quichedood/DAWA-7.x/03-DEV/src/tft.cpp

/*
@file    tft.c
@brief   TFT handling functions for EVE_Test project
@version 1.13
@date    2020-09-05
@author  Rudolph Riedel

@section History

1.0
- initial release

1.1
- added a simple .png image that is drawn beneath the clock just as example of how it could be done

1.2
- replaced the clock with a scrolling line-strip
- moved the .png image over to the font-test section to make room
- added a scrolling bar display
- made scrolling depending on the state of the on/off button
- reduced the precision of VERTEX2F to 1 Pixel with VERTEXT_FORMAT() (FT81x only) to avoid some pointless "*16" multiplications

1.3
- adapted to release 3 of Ft8xx library with EVE_ and ft_ prefixes changed to EVE_
- removed "while (EVE_busy());" lines after EVE_cmd_execute() since it does that by itself now
- removed "EVE_cmd_execute();" line after EVE_cmd_loadimage(MEM_PIC1, EVE_OPT_NODL, pngpic, pngpic_size); as EVE_cmd_loadimage() executes itself now

1.4
- added num_profile_a and num_profile_b for simple profiling
- utilised EVE_cmd_start()
- some general cleanup and house-keeping to make it fit for release

1.5
- simplified the example layout a lot and made it to scale with all display-sizes

1.6
- a bit of house-keeping after trying a couple of things

1.7
- added a display for the amount of bytes generated in the display-list by the command co-pro

1.8
- moved the color settings from EVE_config.h to here

1.9
- changed FT8_ prefixes to EVE_

1.10
- some cleanup

1.11
- updated to be more similar to what I am currently using in projects

1.12
- minor cleanup, switched from EVE_get_touch_tag(1); to EVE_memRead8(REG_TOUCH_TAG);
- added some more sets of calibration data from my displays

1.13
- adapted to V5
- new logo

 */

/*****************************************************
 * ################################################# *
 * ############## Includes ######################### *
 * ################################################# *
*****************************************************/

#include <EVE.h>
#include <Arduino.h>           // Arduino library
#include <Adafruit_MCP23X17.h> // I/O Expander MCP23017 (https://github.com/adafruit/Adafruit-MCP23017-Arduino-Library)
#include <TimeLib.h>           // Time library (https://github.com/PaulStoffregen/Time)
#include <SdFat.h>             // Greiman/SdFat library (https://github.com/greiman/SdFat)
#include <ELMduino.h>          // ELM327 OBD-II library (https://github.com/PowerBroker2/ELMduino)
#include <Adafruit_MLX90614.h> // MLX90614 Infrared temperature sensor (https://github.com/jfitter/MLX90614)
#include <NMEAGPS.h>           // NeoGPS library (https://github.com/SlashDevin/NeoGPS) - In "NeoTime.h" > static const uint16_t s_epoch_year = POSIX_EPOCH_YEAR; static const uint8_t  s_epoch_weekday = POSIX_EPOCH_WEEKDAY;
#include <extEEPROM.h>         // EEPROM library (http://github.com/PaoloP74/extEEPROM)
#include <helper.h>            // DAWA functions helper

/* some pre-definded colors */
#define RED 0xff0000UL
#define ORANGE 0xffa500UL
#define GREEN 0x00ff00UL
#define BLUE 0x0000ffUL
#define BLUE_1 0x5dade2L
#define YELLOW 0xffff00UL
#define PINK 0xff00ffUL
#define PURPLE 0x800080UL
#define WHITE 0xffffffUL
#define BLACK 0x000000UL
#define HEADERS 0x436d79UL

/* memory-map defines */
#define MEM_FONT_01 0
#define MEM_FONT_02 4352
#define MEM_FONT_03 8640
#define MEM_FONT_04 8832
#define MEM_PICT_01 9024 //4352 //5696 //192 //4288 /* start of 100x100 pixel test image, ARGB565, needs 20000 bytes of memory */

#define MEM_DL_STATIC (EVE_RAM_G_SIZE - 4096) /* 0xff000 - start-address of the static part of the display-list, upper 4k of gfx-mem */

uint32_t num_dl_static; /* amount of bytes in the static part of our display-list */
uint8_t tft_active = 0;
uint16_t num_profile_a, num_profile_b;
uint32_t PST_Cmd_n_SpeedMechCmd;
uint32_t tracker_val;

#define LAYOUT_Y1 66

void touch_calibrate(void)
{
  /* send pre-recorded touch calibration values, depending on the display the code is compiled for */
#if defined(EVE_RiTFT43)
  EVE_memWrite32(REG_TOUCH_TRANSFORM_A, 33172);
  EVE_memWrite32(REG_TOUCH_TRANSFORM_B, 123);
  EVE_memWrite32(REG_TOUCH_TRANSFORM_C, 4293527846);
  EVE_memWrite32(REG_TOUCH_TRANSFORM_D, 4294967163);
  EVE_memWrite32(REG_TOUCH_TRANSFORM_E, 4294947501);
  EVE_memWrite32(REG_TOUCH_TRANSFORM_F, 18950047);
#endif

  /* activate this if you are using a module for the first time or if you need to re-calibrate it */
  /* write down the numbers on the screen and either place them in one of the pre-defined blocks above or make a new block */
#if 0
  /* calibrate touch and displays values to screen */
  EVE_cmd_dl(CMD_DLSTART);
  EVE_cmd_dl(DL_CLEAR_RGB | BLACK);
  EVE_cmd_dl(DL_CLEAR | CLR_COL | CLR_STN | CLR_TAG);
  EVE_cmd_text((EVE_HSIZE / 2), 50, 26, EVE_OPT_CENTER, "Please tap on the dot.");
  EVE_cmd_calibrate();
  EVE_cmd_dl(DL_DISPLAY);
  EVE_cmd_dl(CMD_SWAP);
  EVE_cmd_execute();

  uint32_t touch_a, touch_b, touch_c, touch_d, touch_e, touch_f;

  touch_a = EVE_memRead32(REG_TOUCH_TRANSFORM_A);
  touch_b = EVE_memRead32(REG_TOUCH_TRANSFORM_B);
  touch_c = EVE_memRead32(REG_TOUCH_TRANSFORM_C);
  touch_d = EVE_memRead32(REG_TOUCH_TRANSFORM_D);
  touch_e = EVE_memRead32(REG_TOUCH_TRANSFORM_E);
  touch_f = EVE_memRead32(REG_TOUCH_TRANSFORM_F);

  EVE_cmd_dl(CMD_DLSTART);
  EVE_cmd_dl(DL_CLEAR_RGB | BLACK);
  EVE_cmd_dl(DL_CLEAR | CLR_COL | CLR_STN | CLR_TAG);
  EVE_cmd_dl(TAG(0));

  EVE_cmd_text(5, 15, 26, 0, "TOUCH_TRANSFORM_A:");
  EVE_cmd_text(5, 30, 26, 0, "TOUCH_TRANSFORM_B:");
  EVE_cmd_text(5, 45, 26, 0, "TOUCH_TRANSFORM_C:");
  EVE_cmd_text(5, 60, 26, 0, "TOUCH_TRANSFORM_D:");
  EVE_cmd_text(5, 75, 26, 0, "TOUCH_TRANSFORM_E:");
  EVE_cmd_text(5, 90, 26, 0, "TOUCH_TRANSFORM_F:");

  EVE_cmd_setbase(16L);
  EVE_cmd_number(310, 15, 26, EVE_OPT_RIGHTX | 8, touch_a);
  EVE_cmd_number(310, 30, 26, EVE_OPT_RIGHTX | 8, touch_b);
  EVE_cmd_number(310, 45, 26, EVE_OPT_RIGHTX | 8, touch_c);
  EVE_cmd_number(310, 60, 26, EVE_OPT_RIGHTX | 8, touch_d);
  EVE_cmd_number(310, 75, 26, EVE_OPT_RIGHTX | 8, touch_e);
  EVE_cmd_number(310, 90, 26, EVE_OPT_RIGHTX | 8, touch_f);

  EVE_cmd_dl(DL_DISPLAY); /* instruct the graphics processor to show the list */
  EVE_cmd_dl(CMD_SWAP); /* make this list active */
  EVE_cmd_execute();

  while (1);
#endif
}

void initStaticBackground()
{
  EVE_cmd_dl(CMD_DLSTART);      /* Start the display list */
  EVE_cmd_dl(TAG(0));           /* do not use the following objects for touch-detection */
  EVE_cmd_bgcolor(0x00c0c0c0);  /* light grey */
  EVE_cmd_dl(VERTEX_FORMAT(0)); /* reduce precision for VERTEX2F to 1 pixel instead of 1/16 pixel default */

  /* display the logo */
  EVE_cmd_dl(DL_COLOR_RGB | TFT_DEFAULT_FONT_COLOR);
  EVE_cmd_dl(DL_BEGIN | EVE_BITMAPS);
  EVE_cmd_setbitmap(MEM_PICT_01, EVE_COMPRESSED_RGBA_ASTC_4x4_KHR, 480, 272);
  EVE_cmd_dl(VERTEX2F(0, 0));
  EVE_cmd_setfont2(12, MEM_FONT_01, 32);
  EVE_cmd_setfont2(13, MEM_FONT_02, 32);
  EVE_cmd_setfont2(14, MEM_FONT_03, 32);
  EVE_cmd_setfont2(15, MEM_FONT_04, 32);
  EVE_cmd_dl(DL_END);

  while (EVE_busy())
    ;
  num_dl_static = EVE_memRead16(REG_CMD_DL);

  EVE_cmd_memcpy(MEM_DL_STATIC, EVE_RAM_DL, num_dl_static);
  while (EVE_busy())
    ;
}

void TFT_init(void)
{
  if (EVE_init() != 0)
  {
    tft_active = 1;
    EVE_memWrite8(REG_PWM_DUTY, 0x80); /* setup backlight, range is from 0 = off to 0x80 = max */
    touch_calibrate();

    EVE_init_flash();

    /* This is the map of the "009.bin" file burned to the TFT with EVE Asset Builder
    unified.blob                                    : 0      : 4096
    monoMMM_5_12_ASTC.glyph                         : 4096   : 129536
    monoMMM_5_12_ASTC.xfont                         : 133632 : 4352
    monoMMM_5_16_ASTC.glyph                         : 137984 : 129536
    monoMMM_5_16_ASTC.xfont                         : 267520 : 4288
    monoMMM_5_72_ASTC.glyph                         : 271808 : 57344
    monoMMM_5_72_ASTC.xfont                         : 329152 : 192
    carbon_480x272_COMPRESSED_RGBA_ASTC_4x4_KHR.raw : 329344 : 130560
    */

    EVE_cmd_flashread(MEM_FONT_01, 133632, 4352); /* copy from FLASH (read 4288 bits starting offset 84608) to G-RAM (MEM_FONT_01/.xfont) */
    EVE_cmd_flashread(MEM_FONT_02, 267520, 4288);
    EVE_cmd_flashread(MEM_FONT_03, 329152, 192);
    EVE_cmd_flashread(MEM_PICT_01, 329344, 130560);

    initStaticBackground();
  }
}

uint16_t toggle_state = 0;

void TFT_display_setup_buttons(void)
{
  EVE_cmd_dl(DL_COLOR_RGB | WHITE);
  EVE_cmd_fgcolor(0x00c0c0c0); /* some grey */
  EVE_cmd_dl(TAG(50));
  EVE_cmd_button_var(TFT_BUTTON_BORDER_SIZE, EVE_VSIZE - TFT_BUTTON_BORDER_SIZE - TFT_BUTTON_V_SIZE, TFT_BUTTON_H_SIZE, TFT_BUTTON_V_SIZE, 13, EVE_OPT_FORMAT, MENU_BACK, 0);
  EVE_cmd_dl(TAG(51));
  EVE_cmd_button_var(EVE_HSIZE / 4 - TFT_BUTTON_H_SIZE / 2, TFT_BUTTON_V_SIZE * 2, TFT_BUTTON_H_SIZE, TFT_BUTTON_V_SIZE, 13, EVE_OPT_FORMAT, MENU_DIGITAL, 0);
  EVE_cmd_dl(TAG(52));
  EVE_cmd_button_var(EVE_HSIZE / 4 - TFT_BUTTON_H_SIZE / 2, TFT_BUTTON_V_SIZE * 4, TFT_BUTTON_H_SIZE, TFT_BUTTON_V_SIZE, 13, EVE_OPT_FORMAT, MENU_ANALOG, 0);
  EVE_cmd_dl(TAG(53));
  EVE_cmd_button_var(EVE_HSIZE / 4 - TFT_BUTTON_H_SIZE / 2, TFT_BUTTON_V_SIZE * 6, TFT_BUTTON_H_SIZE, TFT_BUTTON_V_SIZE, 13, EVE_OPT_FORMAT, MENU_OBD, 0);
  EVE_cmd_dl(TAG(54));
  EVE_cmd_button_var(EVE_HSIZE * 2 / 4 - TFT_BUTTON_H_SIZE / 2, TFT_BUTTON_V_SIZE * 2, TFT_BUTTON_H_SIZE, TFT_BUTTON_V_SIZE, 13, EVE_OPT_FORMAT, MENU_TEMP, 0);
  EVE_cmd_dl(TAG(55));
  EVE_cmd_button_var(EVE_HSIZE * 2 / 4 - TFT_BUTTON_H_SIZE / 2, TFT_BUTTON_V_SIZE * 4, TFT_BUTTON_H_SIZE, TFT_BUTTON_V_SIZE, 13, EVE_OPT_FORMAT, MENU_GENERAL, 0);
  EVE_cmd_dl(TAG(56));
  EVE_cmd_button_var(EVE_HSIZE * 2 / 4 - TFT_BUTTON_H_SIZE / 2, TFT_BUTTON_V_SIZE * 6, TFT_BUTTON_H_SIZE, TFT_BUTTON_V_SIZE, 13, EVE_OPT_FORMAT, MENU_SDCARD, 0);
  EVE_cmd_dl(TAG(57));
  EVE_cmd_button_var(EVE_HSIZE * 3 / 4 - TFT_BUTTON_H_SIZE / 2, TFT_BUTTON_V_SIZE * 2, TFT_BUTTON_H_SIZE, TFT_BUTTON_V_SIZE, 13, EVE_OPT_FORMAT, MENU_GPS, 0);
  EVE_cmd_dl(TAG(58));
  EVE_cmd_button_var(EVE_HSIZE * 3 / 4 - TFT_BUTTON_H_SIZE / 2, TFT_BUTTON_V_SIZE * 4, TFT_BUTTON_H_SIZE, TFT_BUTTON_V_SIZE, 13, EVE_OPT_FORMAT, MENU_TRACKS, 0);
  EVE_cmd_dl(TAG(59));
  EVE_cmd_button_var(EVE_HSIZE * 3 / 4 - TFT_BUTTON_H_SIZE / 2, TFT_BUTTON_V_SIZE * 6, TFT_BUTTON_H_SIZE, TFT_BUTTON_V_SIZE, 13, EVE_OPT_FORMAT, MENU_EEPROM, 0);
  EVE_cmd_dl(TAG(0));
}

void TFT_display_header(void)
{
  // Display version
  //EVE_cmd_text_var(TFT_DEFAULT_BORDER_H_SIZE, TFT_DEFAULT_BORDER_V_SIZE, 12, EVE_OPT_FORMAT, LABEL_VERSION, 0);

  // Display track
  EVE_cmd_text(TFT_DEFAULT_BORDER_H_SIZE, TFT_DEFAULT_BORDER_V_SIZE, 12, EVE_OPT_FORMAT, LABEL_TRK_UC);
  EVE_cmd_text(TFT_DEFAULT_BORDER_H_SIZE + 33, TFT_DEFAULT_BORDER_V_SIZE, 12, EVE_OPT_FORMAT, g_currentTrack.trackName);
  //EVE_cmd_text_var(TFT_DEFAULT_BORDER_H_SIZE + 100, TFT_DEFAULT_BORDER_V_SIZE, 12, EVE_OPT_FORMAT, "(%d)", 1, g_currentTrackId);

  // Display date/time
  EVE_cmd_text_var(EVE_HSIZE - TFT_DEFAULT_BORDER_H_SIZE, TFT_DEFAULT_BORDER_V_SIZE, 12, EVE_OPT_FORMAT | EVE_OPT_RIGHTX, "%02u/%02u/%02u %02u:%02u:%02u", 6, fix_data.dateTime.date, fix_data.dateTime.month, fix_data.dateTime.year, fix_data.dateTime.hours, fix_data.dateTime.minutes, fix_data.dateTime.seconds);

  // Display GPS signal quality
  if (fix_data.status < 3)
  {
    EVE_color_rgb(RED);
  }
  else
  {
    EVE_color_rgb(GREEN);
  }
  EVE_cmd_text_var(EVE_HSIZE - (TFT_DEFAULT_BORDER_H_SIZE + 150), TFT_DEFAULT_BORDER_V_SIZE, 12, EVE_OPT_FORMAT | EVE_OPT_RIGHTX, "QUAL:%u/4", 1, fix_data.status);
  EVE_color_rgb(TFT_DEFAULT_FONT_COLOR);

  // Display number of GPS acquired sattelites
  if (fix_data.satellites < 6)
  {
    EVE_color_rgb(RED);
  }
  else
  {
    EVE_color_rgb(GREEN);
  }
  EVE_cmd_text_var(EVE_HSIZE - (TFT_DEFAULT_BORDER_H_SIZE + 225), TFT_DEFAULT_BORDER_V_SIZE, 12, EVE_OPT_FORMAT | EVE_OPT_RIGHTX, "SAT:%u", 1, fix_data.satellites);
  EVE_color_rgb(TFT_DEFAULT_FONT_COLOR);
}

void TFT_display_footer(void)
{
  // Display error/information
  if (millis() < g_msgDelay)
  {
    switch (g_msgType)
    {
    case 1: // OK message
      EVE_cmd_dl(COLOR_RGB(0, 255, 0));
      EVE_cmd_dl(DL_BEGIN | EVE_RECTS);
      EVE_cmd_dl(VERTEX2F(EVE_HSIZE / 2 - 175, EVE_VSIZE / 2 - 12));
      EVE_cmd_dl(VERTEX2F(EVE_HSIZE / 2 + 175, EVE_VSIZE / 2 + 8));
      EVE_cmd_dl(DL_END);
      EVE_color_rgb(BLACK);
      break;
    case 2: // ERROR message
      EVE_cmd_dl(COLOR_RGB(255, 0, 0));
      EVE_cmd_dl(DL_BEGIN | EVE_RECTS);
      EVE_cmd_dl(VERTEX2F(EVE_HSIZE / 2 - 175, EVE_VSIZE / 2 - 12));
      EVE_cmd_dl(VERTEX2F(EVE_HSIZE / 2 + 175, EVE_VSIZE / 2 + 8));
      EVE_cmd_dl(DL_END);
      EVE_color_rgb(BLACK);
      break;
    default: // Default message (info)
      EVE_cmd_dl(COLOR_RGB(175, 175, 175));
      EVE_cmd_dl(DL_BEGIN | EVE_RECTS);
      EVE_cmd_dl(VERTEX2F(EVE_HSIZE / 2 - 175, EVE_VSIZE / 2 - 12));
      EVE_cmd_dl(VERTEX2F(EVE_HSIZE / 2 + 175, EVE_VSIZE / 2 + 8));
      EVE_cmd_dl(DL_END);
      EVE_color_rgb(TFT_DEFAULT_FONT_COLOR);
    }
    EVE_cmd_text(EVE_HSIZE / 2, EVE_VSIZE / 2, TFT_FONT_01_SIZE, EVE_OPT_FORMAT | EVE_OPT_CENTERX | EVE_OPT_CENTERY, g_msgLabel);
    EVE_color_rgb(TFT_DEFAULT_FONT_COLOR);
  }
}

/* check for touch events and setup vars for TFT_display() */

/*
g_tftScreenId reference (BUTTON NAME/TAG_ID)
10 : default/start screen (OFF/10, SETUP/11, START/12, LAPS/13)
20 : Screen when running laptimer (STOP/20, FAKELAP/21)
50 : Setup screen (BACK/50, DIGITAL/51, ANALOG/52, OBD/53, TEMP./54, LED/55, SDCARD/56, GPS/57, TRACKS/58, EEPROM/59)
60 : DIGITAL setup (BACK/60)
70 : ANALOG setup (BACK/70)
80 : OBD setup (BACK/80)
90 : TEMP setup (BACK/90, AUTODETECT/91)
100 : GENERAL setup (RPM CORR+/101, RPM CORR-/102, FLYWHEEL T.+/103, FLYWHEEL T.-/104, GEAR CAL./105)
110 : SDCARD setup (BACK/110, IMPORT TRACKS/111)
120 : GPS setup (BACK/120)
130 : TRACKS setup (BACK/130)
140 : EEPROM setup (BACK/140, RESET EEPROM/141, LOAD DEFAULT/142)
150 : LAP TIMES (BACK/150, )
*/
void TFT_touch(void)
{
  uint8_t tag;
  static uint8_t track = 0;
  static uint8_t toggle_lock = 0;

  if (EVE_busy())
  { // is EVE still processing the last display list?
    return;
  }

  tag = EVE_memRead8(REG_TOUCH_TAG); // read the value for the first touch point
  uint32_t touchtest = EVE_memRead32(REG_TOUCH_RAW_XY);

  switch (tag)
  {
  case 0:
    toggle_lock = 0;

    // sliders
    if (touchtest == 0xffffffff) /* display is not touched anymore */
    {
      if (track != 0)
      {
        EVE_cmd_track(0, 0, 0, 0, 0); // stop tracking
        track = 0;
      }
    }
    break;
  case 10: // MAIN > OFF
    if (toggle_lock == 0)
    {
      digitalWrite(powerState, LOW);
    }
    break;
  case 11: // MAIN > SETUP
    if (toggle_lock == 0)
    {
      g_tftScreenId = 50;
      toggle_lock = 1;
      /*if (toggle_state == 0)
      {
        toggle_state = EVE_OPT_FLAT;
      }
      else
      {
        toggle_state = 0;
      }*/
    }
    break;
  case 12: // MAIN > START
    if (toggle_lock == 0)
    {
      g_isRunning = startLaptimer();
      if (g_isRunning >= 1)
      {
        g_tftScreenId = 20;
      }
      toggle_lock = 1;
    }
    break;
  case 13: // MAIN > LAPS
    if (toggle_lock == 0)
    {
      g_tftScreenId = 150;
      toggle_lock = 1;
    }
    break;
  case 20: // MAIN > STOP
    if (toggle_lock == 0)
    {
      switch (g_isRunning)
      {
      case 1:
        g_isRunning = stopLaptimer();
        g_tftScreenId = 10;
        break;
      case 2:
        g_isRunning = stopLaptimer();
        g_tftScreenId = 150;
        break;
      }
      toggle_lock = 1;
    }
    break;
  case 21: // MAIN > FAKELAP
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
      toggle_lock = 1;
    }
    break;
  case 103: // GENERAL > + g_rpmFlywheelTeeth
    if (toggle_lock == 0)
    {
      g_rpmFlywheelTeeth++;
      toggle_lock = 1;
    }
    break;
  case 104: // GENERAL > - g_rpmFlywheelTeeth
    if (toggle_lock == 0)
    {
      g_rpmFlywheelTeeth--;
      toggle_lock = 1;
    }
    break;
  case 105: // GENERAL > Gear calibration
    if (toggle_lock == 0)
    {
      gearCalibration();
      toggle_lock = 1;
    }
    break;
  case 106: // GENERAL > Set ON/OFF OBD features
    if (toggle_lock == 0)
    {
      toggle_lock = 1;
      if (g_enObd == true)
      {
        g_enObd = false;
      }
      else
      {
        g_enObd = true;
      }
    }
    break;
  /*case 100: // LEDs (TEST)
    if (track == 0)
    {
      EVE_cmd_track(80, 80, 200, 40, 100);
      track = 10;
    }
    else
    {
      tracker_val = EVE_memRead32(REG_TRACKER);
      if ((tracker_val & 0xff) == 100)
      {
        tracker_val = tracker_val / 536870;
        PST_Cmd_n_SpeedMechCmd = 8000 - tracker_val;
      }
    }
    break;*/
  case 110: // SDCARD > Back to setup screen
    if (toggle_lock == 0)
    {
      g_tftScreenId = 50;
      toggle_lock = 1;
    }
    break;
  case 111: // SDCARD > Import tracks from SDCARD to EEPROM
    if (toggle_lock == 0)
    {
      if (sd.exists(LABEL_TRACKFILENAME))
      {
        g_trackQty = importTracksFromSd();
        EEPROM_writeAnything(EEPROM_GENERAL_ADDR + 2, (uint8_t)g_trackQty) == sizeof(g_trackQty);
        loadTracksFromEeprom(); // Load track list from EEPROM to RAM
      }
      else // If there is no track file on SD : back to setup menu with error message
      {
        showMessage(LABEL_LOG_NOTRKFILE, 2000, 2);
      }
      g_tftScreenId = 110;
      toggle_lock = 1;
    }
    break;
  case 130: // TRACKS > Back to setup screen
    if (toggle_lock == 0)
    {
      g_tftScreenId = 50;
      toggle_lock = 1;
    }
    break;
  case 131: // TRACKS > Previous tracks
    if (toggle_lock == 0)
    {
      g_trackPage--;
      if (g_trackPage == 255)
      {
        g_trackPage = ceil(g_trackQty / (float)TRACK_PAGINATION) - 1;
      }
      toggle_lock = 1;
    }
    break;
  case 132: // TRACKS > Next tracks
    if (toggle_lock == 0)
    {
      g_trackPage++;
      if (g_trackPage > ceil(g_trackQty / (float)TRACK_PAGINATION) - 1)
      {
        g_trackPage = 0;
      }
      toggle_lock = 1;
    }
    break;
  case 133: // TRACKS > Autoselect track
    if (toggle_lock == 0)
    {
      g_currentTrackId = autoselectTrack();
      loadSelectedTrack(g_currentTrackId);
      EEPROM_writeAnything(EEPROM_GENERAL_ADDR + 5, g_currentTrackId); // Write selected track ID (16 bits)
      toggle_lock = 1;
    }
    break;
  case 140: // EEPROM > Back to setup screen
    if (toggle_lock == 0)
    {
      g_tftScreenId = 50;
      toggle_lock = 1;
    }
    break;
  case 141: // EEPROM > Reset EEPROM
    if (toggle_lock == 0)
    {
      eepromReset();
      eepromReload();
      g_tftScreenId = 140;
      toggle_lock = 1;
    }
    break;
  case 142: // EEPROM > Load default EEPROM values
    if (toggle_lock == 0)
    {
      eepromLoadDefaults();
      eepromReload();
      g_tftScreenId = 140;
      toggle_lock = 1;
    }
    break;
  case 150: // LAPS >  Back to start screen
    if (toggle_lock == 0)
    {
      g_tftScreenId = 10;
      toggle_lock = 1;
    }
    break;
  case 151: // LAPS > Previous laps
    if (toggle_lock == 0)
    {
      g_lapPage--;
      if (g_lapPage == 255)
      {
        g_lapPage = ceil(g_lapQty / (float)LAP_PAGINATION) - 1;
      }
      //loadLapPage(g_lapPage, true);
      toggle_lock = 1;
    }
    break;
  case 152: // LAPS > Next laps
    if (toggle_lock == 0)
    {
      g_lapPage++;
      if (g_lapPage > ceil(g_lapQty / (float)LAP_PAGINATION) - 1)
      {
        g_lapPage = 0;
      }
      //loadLapPage(g_lapPage, true);
      toggle_lock = 1;
    }
    break;
    //case ww:
    /*if (track == 0) //whatever this does, do nothing when tracking is in progress
    {
      //....
    }
    break;*/
  }
}

/*
  dynamic portion of display-handling, meant to be called every 20ms or more
*/
void TFT_display(void)
{
  if (tft_active != 0)
  {
    switch (g_tftScreenId)
    {
    case 10:                                              // default/start screen
      EVE_cmd_dl(CMD_DLSTART);                            /* start the display list */
      EVE_cmd_dl(DL_CLEAR_RGB | BLACK);                   /* set the default clear color to white */
      EVE_cmd_dl(DL_CLEAR | CLR_COL | CLR_STN | CLR_TAG); /* clear the screen - this and the previous prevent artifacts between lists, Attributes are the color, stencil and tag buffers */
      EVE_cmd_dl(TAG(0));

      // insert static part of display-list from copy in gfx-mem
      EVE_cmd_append(MEM_DL_STATIC, num_dl_static);

      // Display date/time
      TFT_display_header();

      // Display button
      EVE_cmd_dl(DL_COLOR_RGB | TFT_DEFAULT_FONT_COLOR);
      EVE_cmd_fgcolor(0x00c0c0c0); /* some grey */
      EVE_cmd_dl(TAG(10));
      EVE_cmd_button_var(TFT_BUTTON_BORDER_SIZE, EVE_VSIZE - TFT_BUTTON_BORDER_SIZE - TFT_BUTTON_V_SIZE, TFT_BUTTON_H_SIZE, TFT_BUTTON_V_SIZE, 13, EVE_OPT_FORMAT, MENU_SHUTDOWN, 0);
      EVE_cmd_dl(TAG(11));
      EVE_cmd_button_var(TFT_BUTTON_BORDER_SIZE + (TFT_BUTTON_H_SPACE + TFT_BUTTON_H_SIZE) * 4, EVE_VSIZE - TFT_BUTTON_BORDER_SIZE - TFT_BUTTON_V_SIZE, TFT_BUTTON_H_SIZE, TFT_BUTTON_V_SIZE, 13, EVE_OPT_FORMAT, MENU_SETUP, 0);
      EVE_cmd_dl(TAG(13));
      EVE_cmd_button_var(TFT_BUTTON_BORDER_SIZE + (TFT_BUTTON_H_SPACE + TFT_BUTTON_H_SIZE) * 1, EVE_VSIZE - TFT_BUTTON_BORDER_SIZE - TFT_BUTTON_V_SIZE, TFT_BUTTON_H_SIZE, TFT_BUTTON_V_SIZE, 13, EVE_OPT_FORMAT, MENU_LAPTIMES, 0);
      EVE_cmd_dl(TAG(12));
      EVE_cmd_fgcolor(GREEN);
      EVE_cmd_button_var(TFT_BUTTON_BORDER_SIZE + (TFT_BUTTON_H_SPACE + TFT_BUTTON_H_SIZE) * 3, EVE_VSIZE - TFT_BUTTON_BORDER_SIZE - TFT_BUTTON_V_SIZE, TFT_BUTTON_H_SIZE, TFT_BUTTON_V_SIZE, 13, EVE_OPT_FORMAT, MENU_START, 0);
      EVE_cmd_dl(TAG(0));
      EVE_cmd_dl(DL_END);

      // Display ...
      EVE_cmd_text_var(TFT_DEFAULT_BORDER_H_SIZE + 10, TFT_FONT_01_V_SPACE + 10, TFT_FONT_03_SIZE, EVE_OPT_FORMAT, "%c", 1, g_anaValuesChar[0]); // GEAR
      EVE_cmd_text_var(EVE_HSIZE - TFT_DEFAULT_BORDER_V_SIZE, 52, TFT_FONT_02_SIZE, EVE_OPT_FORMAT | EVE_OPT_RIGHTX, "%u", 1, (int)g_digValues[0]);       // RPM Acqui : g_digValues[0] / RPM OBD : g_rpm
      EVE_cmd_text_var(EVE_HSIZE - TFT_DEFAULT_BORDER_V_SIZE, 75, TFT_FONT_01_SIZE, EVE_OPT_RIGHTX, LABEL_RPM, 0);
      EVE_cmd_text_var(EVE_HSIZE - TFT_DEFAULT_BORDER_H_SIZE, EVE_VSIZE - 100, TFT_FONT_03_SIZE, EVE_OPT_FORMAT | EVE_OPT_RIGHTX, "%u", 1, (int)fix_data.speed_kph()); // SPEED
      EVE_cmd_text_var(EVE_HSIZE - TFT_DEFAULT_BORDER_V_SIZE, EVE_VSIZE - 39, TFT_FONT_01_SIZE, EVE_OPT_RIGHTX, LABEL_KMH, 0);

      // Infrared temp
      for (uint8_t i = 0; i < MAX_MLX_SIZE; i++)
      {
        if (g_mlxAddresses[i] != 0x00)
        {
          if ((int)round(g_mlxValues[i]) < 200)
          {
            EVE_cmd_text_var(TFT_DEFAULT_BORDER_H_SIZE + (i * 60), 210, TFT_FONT_01_SIZE, EVE_OPT_FORMAT, "T%u:%u°", 2, g_mlxAddresses[i], (int)round(g_mlxValues[i]));
          }
          else
          {
            EVE_cmd_text_var(TFT_DEFAULT_BORDER_H_SIZE + (i * 60), 210, TFT_FONT_01_SIZE, EVE_OPT_FORMAT, "T%u:HOT!", 1, g_mlxAddresses[i]);
          }
        }
      }

      // RPM
      EVE_cmd_dl(COLOR_RGB(67, 109, 121));
      EVE_cmd_dl(DL_BEGIN | EVE_LINES);
      for (uint8_t i = 0; i <= 16; i++)
      {
        EVE_cmd_dl(VERTEX2F((i * 25) + 70, 42));
        EVE_cmd_dl(VERTEX2F((i * 25) + 70, 48));
      }
      EVE_cmd_dl(DL_END);
      for (uint8_t i = 0; i <= 16; i++)
      {
        EVE_cmd_text_var((i * 25) + 70, 25, TFT_FONT_01_SIZE, EVE_OPT_FORMAT | EVE_OPT_CENTERX, "%u", 1, i);
      }
      EVE_cmd_dl(SCISSOR_XY(70, 48));                      // Limit drawing area (X, Y)
      EVE_cmd_dl(SCISSOR_SIZE(((int)g_digValues[0] / 40), 25));          // Limit drawing area (W, H) //g_digValues[0]
      EVE_cmd_gradient(75, 0, 0x436d79, 470, 0, 0x2effff); // Don't bother with "Y", Xstart and Xend
      EVE_cmd_dl(SCISSOR_XY(0, 0));                        // Restore full drawing area (X, Y)
      EVE_cmd_dl(SCISSOR_SIZE(EVE_HSIZE, EVE_VSIZE));      // Restore full area (W, H)
      /*
      EVE_cmd_dl(COLOR_RGB(0, 255, 0));
      uint16_t rpmBarPos;
      for (uint8_t i = 0; i <= 36; i++)
      {
        if (i < 35) // Last 2 bar have same position
        {
          rpmBarPos = (int)(log(i + 2) * 20); // +2 to have a nice log curve
        }
        if (g_digValues[0] >= i * 500)
        {
          if (i < 25)
          {
            EVE_cmd_dl(COLOR_RGB(0, 255, 0));
            //EVE_cmd_dl(COLOR_A(128));
          }
          else
          {
            EVE_cmd_dl(COLOR_RGB(255, 0, 0));
          }
          EVE_cmd_dl(BEGIN(EVE_RECTS));
          EVE_cmd_dl(VERTEX2F((i * 9) + 100, 150 - rpmBarPos));
          EVE_cmd_dl(VERTEX2F((i * 9) + 105, 100 - rpmBarPos));
        }
        else
        {
          EVE_cmd_dl(COLOR_RGB(150, 150, 150));
          EVE_cmd_dl(BEGIN(EVE_RECTS));
          EVE_cmd_dl(VERTEX2F((i * 9) + 100, 150 - rpmBarPos));
          EVE_cmd_dl(VERTEX2F((i * 9) + 105, 100 - rpmBarPos));
        }
        if ((i * 500) % 1000 == 0)
        {
          EVE_cmd_text_var((i * 9) + 100, 150 - rpmBarPos + 10, TFT_FONT_01_SIZE, EVE_OPT_FORMAT | EVE_OPT_CENTERX, "%u", 1, (i / 2));
        }
      }*/

      // Display footer
      TFT_display_footer();
      break;
    case 20:                                              // Screen when running laptimer (show "STOP" button)
      EVE_cmd_dl(CMD_DLSTART);                            /* start the display list */
      EVE_cmd_dl(DL_CLEAR_RGB | BLACK);                   /* set the default clear color to white */
      EVE_cmd_dl(DL_CLEAR | CLR_COL | CLR_STN | CLR_TAG); /* clear the screen - this and the previous prevent artifacts between lists, Attributes are the color, stencil and tag buffers */
      EVE_cmd_dl(TAG(0));

      // insert static part of display-list from copy in gfx-mem
      EVE_cmd_append(MEM_DL_STATIC, num_dl_static);

      // Display date/time
      TFT_display_header();

      // Display button
      EVE_cmd_dl(DL_COLOR_RGB | TFT_DEFAULT_FONT_COLOR);
      EVE_cmd_fgcolor(0x00c0c0c0); /* some grey */
      if (g_isRunning == 2)
      {
        EVE_cmd_dl(TAG(21));
        EVE_cmd_button_var(TFT_BUTTON_BORDER_SIZE + (TFT_BUTTON_H_SPACE + TFT_BUTTON_H_SIZE) * 3, EVE_VSIZE - TFT_BUTTON_BORDER_SIZE - TFT_BUTTON_V_SIZE, TFT_BUTTON_H_SIZE, TFT_BUTTON_V_SIZE, 13, EVE_OPT_FORMAT, MENU_FAKELAP, 0);
      }
      EVE_cmd_dl(TAG(20));
      EVE_cmd_fgcolor(RED);
      EVE_cmd_button_var(TFT_BUTTON_BORDER_SIZE + (TFT_BUTTON_H_SPACE + TFT_BUTTON_H_SIZE) * 2, EVE_VSIZE - TFT_BUTTON_BORDER_SIZE - TFT_BUTTON_V_SIZE, TFT_BUTTON_H_SIZE, TFT_BUTTON_V_SIZE, 13, EVE_OPT_FORMAT, MENU_STOP, 0);
      EVE_cmd_dl(TAG(0)); /* no touch */

      // Display ...
      EVE_cmd_text_var(TFT_DEFAULT_BORDER_H_SIZE + 10, TFT_FONT_01_V_SPACE + 10, TFT_FONT_03_SIZE, EVE_OPT_FORMAT, "%c", 1, g_anaValuesChar[0]); // GEAR
      if (g_isRunning == 2)
      {
        if (g_lapQty > 0)
        {
          // Print current lap
          EVE_cmd_text_var(EVE_HSIZE / 6, EVE_VSIZE / 3, TFT_FONT_03_SIZE, EVE_OPT_FORMAT, "%02u:%02u:%u", 3, g_currentLap.lapTimeS / 60, g_currentLap.lapTimeS % 60, g_currentLap.lapTimeCs / 10);

          // Print last 3 history laps
          for (uint8_t i = 1; i < constrain(g_lapQty, 1, 4); i++)
          {
            EVE_cmd_text_var(EVE_HSIZE / 2, EVE_VSIZE * 1 / 2 + (TFT_FONT_02_V_SPACE * i), TFT_FONT_02_SIZE, EVE_OPT_FORMAT | EVE_OPT_CENTERX, "LAP %u > %02u:%02u:%02u", 4, g_lapsList[g_lapQty - i].lapNumber, g_lapsList[g_lapQty - i].lapTimeS / 60, g_lapsList[g_lapQty - i].lapTimeS % 60, g_lapsList[g_lapQty - i].lapTimeCs);
          }
        }
        else
        {
          // Lap 0, waiting for finish line crossing for the first time ...
          EVE_cmd_text(EVE_HSIZE / 2, EVE_VSIZE / 2, TFT_FONT_02_SIZE, EVE_OPT_CENTERX | EVE_OPT_CENTERY, LABEL_READY_TO_GO);
        }
      }
      EVE_cmd_text_var(EVE_HSIZE - TFT_DEFAULT_BORDER_V_SIZE, 52, TFT_FONT_02_SIZE, EVE_OPT_FORMAT | EVE_OPT_RIGHTX, "%u", 1, (int)g_digValues[0]);       // RPM Acqui : g_digValues[0] / RPM OBD : g_rpm
      EVE_cmd_text_var(EVE_HSIZE - TFT_DEFAULT_BORDER_V_SIZE, 75, TFT_FONT_01_SIZE, EVE_OPT_RIGHTX, LABEL_RPM, 0);
      EVE_cmd_text_var(EVE_HSIZE - TFT_DEFAULT_BORDER_H_SIZE, EVE_VSIZE - 100, TFT_FONT_03_SIZE, EVE_OPT_FORMAT | EVE_OPT_RIGHTX, "%u", 1, (int)fix_data.speed_kph()); // SPEED
      EVE_cmd_text_var(EVE_HSIZE - TFT_DEFAULT_BORDER_V_SIZE, EVE_VSIZE - 39, TFT_FONT_01_SIZE, EVE_OPT_RIGHTX, LABEL_KMH, 0);

      // Infrared temp
      for (uint8_t i = 0; i < MAX_MLX_SIZE; i++)
      {
        if (g_mlxAddresses[i] != 0x00)
        {
          if ((int)round(g_mlxValues[i]) < 200)
          {
            EVE_cmd_text_var(TFT_DEFAULT_BORDER_H_SIZE + (i * 60), 210, TFT_FONT_01_SIZE, EVE_OPT_FORMAT, "T%u:%u°", 2, g_mlxAddresses[i], (int)round(g_mlxValues[i]));
          }
          else
          {
            EVE_cmd_text_var(TFT_DEFAULT_BORDER_H_SIZE + (i * 60), 210, TFT_FONT_01_SIZE, EVE_OPT_FORMAT, "T%u:HOT!", 1, g_mlxAddresses[i]);
          }
        }
      }

      // RPM
      EVE_cmd_dl(COLOR_RGB(67, 109, 121));
      EVE_cmd_dl(DL_BEGIN | EVE_LINES);
      for (uint8_t i = 0; i <= 16; i++)
      {
        EVE_cmd_dl(VERTEX2F((i * 25) + 70, 42));
        EVE_cmd_dl(VERTEX2F((i * 25) + 70, 48));
      }
      EVE_cmd_dl(DL_END);
      for (uint8_t i = 0; i <= 16; i++)
      {
        EVE_cmd_text_var((i * 25) + 70, 25, TFT_FONT_01_SIZE, EVE_OPT_FORMAT | EVE_OPT_CENTERX, "%u", 1, i);
      }
      EVE_cmd_dl(SCISSOR_XY(70, 48));                      // Limit drawing area (X, Y)
      EVE_cmd_dl(SCISSOR_SIZE(((int)g_digValues[0] / 40), 25)); // Limit drawing area (W, H)
      EVE_cmd_gradient(75, 0, 0x436d79, 470, 0, 0x2effff); // Don't bother with "Y", Xstart and Xend
      EVE_cmd_dl(SCISSOR_XY(0, 0));                        // Restore full drawing area (X, Y)
      EVE_cmd_dl(SCISSOR_SIZE(EVE_HSIZE, EVE_VSIZE));      // Restore full area (W, H)

      // Display footer
      TFT_display_footer();
      break;
    case 50:                                              // Setup screen (show all subcategories for configuration)
      EVE_cmd_dl(CMD_DLSTART);                            /* start the display list */
      EVE_cmd_dl(DL_CLEAR_RGB | BLACK);                   /* set the default clear color to white */
      EVE_cmd_dl(DL_CLEAR | CLR_COL | CLR_STN | CLR_TAG); /* clear the screen - this and the previous prevent artifacts between lists, Attributes are the color, stencil and tag buffers */
      EVE_cmd_dl(TAG(0));

      // insert static part of display-list from copy in gfx-mem
      EVE_cmd_append(MEM_DL_STATIC, num_dl_static);

      // Display date/time
      TFT_display_header();

      // Display setup menu buttons
      TFT_display_setup_buttons();

      // Display footer
      TFT_display_footer();
      break;
    case 60:                                              // DIGITAL setup
      EVE_cmd_dl(CMD_DLSTART);                            /* start the display list */
      EVE_cmd_dl(DL_CLEAR_RGB | BLACK);                   /* set the default clear color to white */
      EVE_cmd_dl(DL_CLEAR | CLR_COL | CLR_STN | CLR_TAG); /* clear the screen - this and the previous prevent artifacts between lists, Attributes are the color, stencil and tag buffers */
      EVE_cmd_dl(TAG(0));

      // insert static part of display-list from copy in gfx-mem
      EVE_cmd_append(MEM_DL_STATIC, num_dl_static);

      // Display date/time
      TFT_display_header();

      // Parse 4 digital inputs (label + on/off button)
      for (uint8_t i = 0; i < 4; i++)
      {
        EVE_cmd_text(EVE_HSIZE / 4, TFT_HEADER_V_SPACE + (i * (TFT_FONT_02_V_SPACE + 8)), TFT_FONT_02_SIZE, EVE_OPT_FORMAT, digitalInputsLabel[i]);
        EVE_cmd_dl(TAG(61 + i));
        EVE_cmd_toggle(EVE_HSIZE * 2 / 4, TFT_HEADER_V_SPACE + (i * (TFT_FONT_02_V_SPACE + 8)), 40, TFT_FONT_02_SIZE, 0, (bitRead(g_enDigitalInputsBits, i) == true) ? 65535 : 0, "OFF\xffON");
        EVE_cmd_dl(TAG(0));
        if (bitRead(g_enDigitalInputsBits, i) == true)
        {
          EVE_cmd_text_var(EVE_HSIZE * 3 / 4, TFT_HEADER_V_SPACE + (i * (TFT_FONT_02_V_SPACE + 8)), TFT_FONT_02_SIZE, EVE_OPT_FORMAT, "(%d)", 1, g_digValues[i]);
        }
      }

      // Display setup menu buttons
      EVE_cmd_dl(DL_COLOR_RGB | WHITE);
      EVE_cmd_fgcolor(0x00c0c0c0); /* some grey */
      EVE_cmd_dl(TAG(65));
      EVE_cmd_button_var(TFT_BUTTON_BORDER_SIZE, EVE_VSIZE - TFT_BUTTON_BORDER_SIZE - TFT_BUTTON_V_SIZE, TFT_BUTTON_H_SIZE, TFT_BUTTON_V_SIZE, TFT_FONT_02_SIZE, EVE_OPT_FORMAT, MENU_BACK, 0);
      EVE_cmd_dl(TAG(0));

      // Display footer
      TFT_display_footer();
      break;
    case 70:                                              // ANALOG setup
      EVE_cmd_dl(CMD_DLSTART);                            /* start the display list */
      EVE_cmd_dl(DL_CLEAR_RGB | BLACK);                   /* set the default clear color to white */
      EVE_cmd_dl(DL_CLEAR | CLR_COL | CLR_STN | CLR_TAG); /* clear the screen - this and the previous prevent artifacts between lists, Attributes are the color, stencil and tag buffers */
      EVE_cmd_dl(TAG(0));

      // insert static part of display-list from copy in gfx-mem
      EVE_cmd_append(MEM_DL_STATIC, num_dl_static);

      // Display date/time
      TFT_display_header();

      // Parse 8 analog inputs (label + on/off button)
      for (uint8_t i = 0; i < 8; i++)
      {
        EVE_cmd_text(EVE_HSIZE / 4, TFT_HEADER_V_SPACE + (i * (TFT_FONT_02_V_SPACE + 8)), TFT_FONT_02_SIZE, EVE_OPT_FORMAT, analogInputsLabel[i]);
        EVE_cmd_dl(TAG(71 + i));
        EVE_cmd_toggle(EVE_HSIZE * 2 / 4, TFT_HEADER_V_SPACE + (i * (TFT_FONT_02_V_SPACE + 8)), 40, TFT_FONT_02_SIZE, 0, (bitRead(g_enAnalogInputsBits, i) == true) ? 65535 : 0, "OFF\xffON");
        EVE_cmd_dl(TAG(0));
        if (bitRead(g_enAnalogInputsBits, i) == true)
        {
          EVE_cmd_text_var(EVE_HSIZE * 3 / 4, TFT_HEADER_V_SPACE + (i * (TFT_FONT_02_V_SPACE + 8)), TFT_FONT_02_SIZE, EVE_OPT_FORMAT, "(%d)", 1, g_anaValues[i]);
        }
      }

      // Display setup menu buttons
      EVE_cmd_dl(DL_COLOR_RGB | WHITE);
      EVE_cmd_fgcolor(0x00c0c0c0); /* some grey */
      EVE_cmd_dl(TAG(79));
      EVE_cmd_button_var(TFT_BUTTON_BORDER_SIZE, EVE_VSIZE - TFT_BUTTON_BORDER_SIZE - TFT_BUTTON_V_SIZE, TFT_BUTTON_H_SIZE, TFT_BUTTON_V_SIZE, TFT_FONT_02_SIZE, EVE_OPT_FORMAT, MENU_BACK, 0);
      EVE_cmd_dl(TAG(0));

      // Display footer
      TFT_display_footer();
      break;
    case 80:                                              // OBD setup
      EVE_cmd_dl(CMD_DLSTART);                            /* start the display list */
      EVE_cmd_dl(DL_CLEAR_RGB | BLACK);                   /* set the default clear color to white */
      EVE_cmd_dl(DL_CLEAR | CLR_COL | CLR_STN | CLR_TAG); /* clear the screen - this and the previous prevent artifacts between lists, Attributes are the color, stencil and tag buffers */
      EVE_cmd_dl(TAG(0));

      // insert static part of display-list from copy in gfx-mem
      EVE_cmd_append(MEM_DL_STATIC, num_dl_static);

      // Display date/time
      TFT_display_header();

      EVE_color_rgb(HEADERS);
      EVE_cmd_text(EVE_HSIZE / 12 * 2, TFT_HEADER_V_SPACE, TFT_FONT_02_SIZE, EVE_OPT_FORMAT, "NAME");
      EVE_cmd_text(EVE_HSIZE / 12 * 6, TFT_HEADER_V_SPACE, TFT_FONT_02_SIZE, EVE_OPT_FORMAT, "VALUES");
      EVE_color_rgb(TFT_DEFAULT_FONT_COLOR);

      EVE_cmd_text(EVE_HSIZE / 12 * 2, TFT_HEADER_V_SPACE_HEADER + TFT_FONT_02_V_SPACE * 0, TFT_FONT_02_SIZE, EVE_OPT_FORMAT, "RPM");
      EVE_cmd_text(EVE_HSIZE / 12 * 2, TFT_HEADER_V_SPACE_HEADER + TFT_FONT_02_V_SPACE * 1, TFT_FONT_02_SIZE, EVE_OPT_FORMAT, "COOLANT");

      EVE_cmd_text_var(EVE_HSIZE / 12 * 6, TFT_HEADER_V_SPACE_HEADER + TFT_FONT_02_V_SPACE * 0, TFT_FONT_02_SIZE, EVE_OPT_FORMAT, "%u rpm", 1, g_rpm);
      EVE_cmd_text_var(EVE_HSIZE / 12 * 6, TFT_HEADER_V_SPACE_HEADER + TFT_FONT_02_V_SPACE * 1, TFT_FONT_02_SIZE, EVE_OPT_FORMAT, "%u deg", 1, g_engineCoolantT);

      // Display setup menu buttons
      EVE_cmd_dl(DL_COLOR_RGB | WHITE);
      EVE_cmd_fgcolor(0x00c0c0c0); /* some grey */
      EVE_cmd_dl(TAG(80));
      EVE_cmd_button_var(TFT_BUTTON_BORDER_SIZE, EVE_VSIZE - TFT_BUTTON_BORDER_SIZE - TFT_BUTTON_V_SIZE, TFT_BUTTON_H_SIZE, TFT_BUTTON_V_SIZE, TFT_FONT_02_SIZE, EVE_OPT_FORMAT, MENU_BACK, 0);
      EVE_cmd_dl(TAG(0));

      // Display footer
      TFT_display_footer();
      break;
    case 90:                                              // TEMP sensors setup
      EVE_cmd_dl(CMD_DLSTART);                            /* start the display list */
      EVE_cmd_dl(DL_CLEAR_RGB | BLACK);                   /* set the default clear color to white */
      EVE_cmd_dl(DL_CLEAR | CLR_COL | CLR_STN | CLR_TAG); /* clear the screen - this and the previous prevent artifacts between lists, Attributes are the color, stencil and tag buffers */
      EVE_cmd_dl(TAG(0));

      // insert static part of display-list from copy in gfx-mem
      EVE_cmd_append(MEM_DL_STATIC, num_dl_static);

      // Display date/time
      TFT_display_header();

      // Display ...
      // Parse the MAX_MLX_SIZE MLX sensors
      for (uint8_t i = 0; i < MAX_MLX_SIZE; i++)
      {
        if (g_mlxAddresses[i] != 0x00)
        {
          if ((int)round(g_mlxValues[i]) < 200)
          {
            EVE_cmd_text_var(TFT_DEFAULT_BORDER_H_SIZE + 50, TFT_HEADER_V_SPACE + (i * (TFT_FONT_02_V_SPACE + 8)), TFT_FONT_02_SIZE, EVE_OPT_FORMAT, "Temp. sensor %u : %u°", 2, g_mlxAddresses[i], (int)round(g_mlxValues[i]));
          }
          else
          {
            EVE_cmd_text_var(TFT_DEFAULT_BORDER_H_SIZE + 50, TFT_HEADER_V_SPACE + (i * (TFT_FONT_02_V_SPACE + 8)), TFT_FONT_02_SIZE, EVE_OPT_FORMAT, "Temp. sensor %u : HOT!", 1, g_mlxAddresses[i]);
          }
        }
      }

      // Display setup menu buttons
      EVE_cmd_dl(DL_COLOR_RGB | WHITE);
      EVE_cmd_fgcolor(0x00c0c0c0); /* some grey */
      EVE_cmd_dl(TAG(90));
      EVE_cmd_button_var(TFT_BUTTON_BORDER_SIZE, EVE_VSIZE - TFT_BUTTON_BORDER_SIZE - TFT_BUTTON_V_SIZE, TFT_BUTTON_H_SIZE, TFT_BUTTON_V_SIZE, TFT_FONT_02_SIZE, EVE_OPT_FORMAT, MENU_BACK, 0);
      EVE_cmd_dl(TAG(91));
      EVE_cmd_button_var(TFT_BUTTON_BORDER_SIZE + (TFT_BUTTON_H_SIZE + TFT_BUTTON_H_SPACE), EVE_VSIZE - TFT_BUTTON_BORDER_SIZE - TFT_BUTTON_V_SIZE, TFT_BUTTON_H2_SIZE, TFT_BUTTON_V_SIZE, TFT_FONT_02_SIZE, EVE_OPT_FORMAT, MENU_AUTODETECT_MLX, 0);
      EVE_cmd_dl(TAG(0));

      // Display footer
      TFT_display_footer();
      break;
    case 100:                                             // GENERAL setup
      EVE_cmd_dl(CMD_DLSTART);                            /* start the display list */
      EVE_cmd_dl(DL_CLEAR_RGB | BLACK);                   /* set the default clear color to white */
      EVE_cmd_dl(DL_CLEAR | CLR_COL | CLR_STN | CLR_TAG); /* clear the screen - this and the previous prevent artifacts between lists, Attributes are the color, stencil and tag buffers */
      EVE_cmd_dl(TAG(0));

      // insert static part of display-list from copy in gfx-mem
      EVE_cmd_append(MEM_DL_STATIC, num_dl_static);

      // Display date/time
      TFT_display_header();

      // Display ...

      // Display setup menu buttons
      EVE_cmd_dl(DL_COLOR_RGB | WHITE);
      EVE_cmd_fgcolor(0x00c0c0c0); /* some grey */
      EVE_cmd_dl(TAG(100));
      EVE_cmd_button_var(TFT_BUTTON_BORDER_SIZE, EVE_VSIZE - TFT_BUTTON_BORDER_SIZE - TFT_BUTTON_V_SIZE, TFT_BUTTON_H_SIZE, TFT_BUTTON_V_SIZE, TFT_FONT_02_SIZE, EVE_OPT_FORMAT, MENU_BACK, 0);
      EVE_cmd_dl(TAG(0));

      EVE_cmd_text_var(EVE_HSIZE / 12, TFT_HEADER_V_SPACE + (0 * (TFT_FONT_02_V_SPACE + 8)), TFT_FONT_02_SIZE, EVE_OPT_FORMAT, "RPM Correction ratio : %u", 1, g_rpmCorrectionRatio);
      EVE_cmd_text_var(EVE_HSIZE / 12, TFT_HEADER_V_SPACE + (1 * (TFT_FONT_02_V_SPACE + 8)), TFT_FONT_02_SIZE, EVE_OPT_FORMAT, "RPM Flywheel teeth : %u", 1, g_rpmFlywheelTeeth);
      EVE_cmd_text(EVE_HSIZE / 12, TFT_HEADER_V_SPACE + (2 * (TFT_FONT_02_V_SPACE + 8)), TFT_FONT_02_SIZE, EVE_OPT_FORMAT, "Gear calibration : ");
      EVE_cmd_text(EVE_HSIZE / 12, TFT_HEADER_V_SPACE + (4 * (TFT_FONT_02_V_SPACE + 8)), TFT_FONT_02_SIZE, EVE_OPT_FORMAT, "OBD features : ");

      EVE_cmd_dl(TAG(102));
      EVE_cmd_button_var(EVE_HSIZE / 12 * 10, TFT_HEADER_V_SPACE + (0 * (TFT_FONT_02_V_SPACE + 8)), TFT_BUTTON_H3_SIZE, TFT_BUTTON_V3_SIZE, TFT_FONT_02_SIZE, EVE_OPT_FORMAT, "-", 0);
      EVE_cmd_dl(TAG(101));
      EVE_cmd_button_var(EVE_HSIZE / 12 * 11, TFT_HEADER_V_SPACE + (0 * (TFT_FONT_02_V_SPACE + 8)), TFT_BUTTON_H3_SIZE, TFT_BUTTON_V3_SIZE, TFT_FONT_02_SIZE, EVE_OPT_FORMAT, "+", 0);

      EVE_cmd_dl(TAG(104));
      EVE_cmd_button_var(EVE_HSIZE / 12 * 10, TFT_HEADER_V_SPACE + (1 * (TFT_FONT_02_V_SPACE + 8)), TFT_BUTTON_H3_SIZE, TFT_BUTTON_V3_SIZE, TFT_FONT_02_SIZE, EVE_OPT_FORMAT, "-", 0);
      EVE_cmd_dl(TAG(103));
      EVE_cmd_button_var(EVE_HSIZE / 12 * 11, TFT_HEADER_V_SPACE + (1 * (TFT_FONT_02_V_SPACE + 8)), TFT_BUTTON_H3_SIZE, TFT_BUTTON_V3_SIZE, TFT_FONT_02_SIZE, EVE_OPT_FORMAT, "+", 0);

      EVE_cmd_dl(TAG(105));
      EVE_cmd_button_var(EVE_HSIZE / 12 * 10, TFT_HEADER_V_SPACE + (2 * (TFT_FONT_02_V_SPACE + 8)), TFT_BUTTON_H4_SIZE, TFT_BUTTON_V3_SIZE, TFT_FONT_02_SIZE, EVE_OPT_FORMAT, "SET", 0);
      EVE_cmd_dl(TAG(0));

      EVE_cmd_dl(TAG(106));
      EVE_cmd_toggle(EVE_HSIZE / 12 * 10, TFT_HEADER_V_SPACE + (4 * (TFT_FONT_02_V_SPACE + 8)), 40, TFT_FONT_02_SIZE, 0, (g_enObd == true) ? 65535 : 0, "OFF\xffON");
      EVE_cmd_dl(TAG(0));

      // Display footer
      TFT_display_footer();
      break;
    /*case 100:                                             // LEDS setup
      EVE_cmd_dl(CMD_DLSTART);                            
      EVE_cmd_dl(DL_CLEAR_RGB | BLACK);                   
      EVE_cmd_dl(DL_CLEAR | CLR_COL | CLR_STN | CLR_TAG); 
      EVE_cmd_dl(TAG(0));

      //EVE_color_rgb(YELLOW);
      //EVE_cmd_dl(LINE_WIDTH(1 * 16));
      //EVE_cmd_dl(DL_BEGIN | EVE_RECTS);
      //EVE_cmd_dl(TAG(40));
      //EVE_cmd_dl(VERTEX2F(1280, 1280)); // 80,80
      //EVE_cmd_dl(VERTEX2F(4480, 1920)); // 280,120
      //EVE_cmd_dl(TAG(0));
      //EVE_cmd_dl(DL_END);

      EVE_cmd_dl(TAG(100));
      EVE_cmd_slider(80, 80, 200, 10, 0, 8000 - PST_Cmd_n_SpeedMechCmd, 8000); 
      EVE_cmd_dl(TAG(0));

      EVE_cmd_text_var(TFT_DEFAULT_BORDER_H_SIZE, TFT_DEFAULT_BORDER_V_SIZE + (TFT_FONT_01_V_SPACE)*1, TFT_FONT_01_SIZE, EVE_OPT_FORMAT, "slider : %u", 1, tracker_val);

      // Display setup menu buttons
      EVE_cmd_dl(DL_COLOR_RGB | WHITE);
      EVE_cmd_fgcolor(0x00c0c0c0);
      EVE_cmd_dl(TAG(50));
      EVE_cmd_button_var(TFT_BUTTON_BORDER_SIZE, EVE_VSIZE - TFT_BUTTON_BORDER_SIZE - TFT_BUTTON_V_SIZE, TFT_BUTTON_H_SIZE, TFT_BUTTON_V_SIZE, 13, EVE_OPT_FORMAT, MENU_BACK, 0);
      EVE_cmd_dl(TAG(0));
      break;*/
    case 110:                                             // SDCARD setup
      EVE_cmd_dl(CMD_DLSTART);                            /* start the display list */
      EVE_cmd_dl(DL_CLEAR_RGB | BLACK);                   /* set the default clear color to white */
      EVE_cmd_dl(DL_CLEAR | CLR_COL | CLR_STN | CLR_TAG); /* clear the screen - this and the previous prevent artifacts between lists, Attributes are the color, stencil and tag buffers */
      EVE_cmd_dl(TAG(0));

      // insert static part of display-list from copy in gfx-mem
      EVE_cmd_append(MEM_DL_STATIC, num_dl_static);

      // Display date/time
      TFT_display_header();

      // Display ...

      // TODO ...

      // Display setup menu buttons
      EVE_cmd_dl(DL_COLOR_RGB | WHITE);
      EVE_cmd_fgcolor(0x00c0c0c0); /* some grey */
      EVE_cmd_dl(TAG(110));
      EVE_cmd_button_var(TFT_BUTTON_BORDER_SIZE, EVE_VSIZE - TFT_BUTTON_BORDER_SIZE - TFT_BUTTON_V_SIZE, TFT_BUTTON_H_SIZE, TFT_BUTTON_V_SIZE, TFT_FONT_02_SIZE, EVE_OPT_FORMAT, MENU_BACK, 0);
      EVE_cmd_dl(TAG(111));
      EVE_cmd_button_var(TFT_BUTTON_BORDER_SIZE + (TFT_BUTTON_H_SIZE + TFT_BUTTON_H_SPACE), EVE_VSIZE - TFT_BUTTON_BORDER_SIZE - TFT_BUTTON_V_SIZE, TFT_BUTTON_H2_SIZE, TFT_BUTTON_V_SIZE, TFT_FONT_02_SIZE, EVE_OPT_FORMAT, MENU_IMPORT_TRACK, 0);
      EVE_cmd_dl(TAG(0));

      // Display footer
      TFT_display_footer();
      break;
    case 120:                                             // GPS setup
      EVE_cmd_dl(CMD_DLSTART);                            /* start the display list */
      EVE_cmd_dl(DL_CLEAR_RGB | BLACK);                   /* set the default clear color to white */
      EVE_cmd_dl(DL_CLEAR | CLR_COL | CLR_STN | CLR_TAG); /* clear the screen - this and the previous prevent artifacts between lists, Attributes are the color, stencil and tag buffers */
      EVE_cmd_dl(TAG(0));

      // insert static part of display-list from copy in gfx-mem
      EVE_cmd_append(MEM_DL_STATIC, num_dl_static);

      // Display date/time
      TFT_display_header();

      EVE_cmd_text_var(EVE_HSIZE / 4, TFT_HEADER_V_SPACE, TFT_FONT_02_SIZE, EVE_OPT_FORMAT, "Latitude : %u.%u°", 2, fix_data.latitudeL() / 10000000, fix_data.latitudeL() % 10000000);
      EVE_cmd_text_var(EVE_HSIZE / 4, TFT_HEADER_V_SPACE + TFT_FONT_02_V_SPACE * 1, TFT_FONT_02_SIZE, EVE_OPT_FORMAT, "Longitude : %u.%u°", 2, fix_data.longitudeL() / 10000000, fix_data.longitudeL() % 10000000);
      EVE_cmd_text_var(EVE_HSIZE / 4, TFT_HEADER_V_SPACE + TFT_FONT_02_V_SPACE * 2, TFT_FONT_02_SIZE, EVE_OPT_FORMAT, "Altitude : %um", 1, fix_data.alt.whole);
      EVE_cmd_text_var(EVE_HSIZE / 4, TFT_HEADER_V_SPACE + TFT_FONT_02_V_SPACE * 3, TFT_FONT_02_SIZE, EVE_OPT_FORMAT, "Speed : %ukm/h", 1, (int)fix_data.speed_kph());
      EVE_cmd_text_var(EVE_HSIZE / 4, TFT_HEADER_V_SPACE + TFT_FONT_02_V_SPACE * 4, TFT_FONT_02_SIZE, EVE_OPT_FORMAT, "Satellites : %u", 1, fix_data.satellites);
      EVE_cmd_text_var(EVE_HSIZE / 4, TFT_HEADER_V_SPACE + TFT_FONT_02_V_SPACE * 5, TFT_FONT_02_SIZE, EVE_OPT_FORMAT, "Heading : %u°", 1, (int)fix_data.heading());
      EVE_cmd_text_var(EVE_HSIZE / 4, TFT_HEADER_V_SPACE + TFT_FONT_02_V_SPACE * 6, TFT_FONT_02_SIZE, EVE_OPT_FORMAT, "Quality : %u/4", 1, fix_data.status);

      // Display setup menu buttons
      EVE_cmd_dl(DL_COLOR_RGB | WHITE);
      EVE_cmd_fgcolor(0x00c0c0c0); /* some grey */
      EVE_cmd_dl(TAG(140));
      EVE_cmd_button_var(TFT_BUTTON_BORDER_SIZE, EVE_VSIZE - TFT_BUTTON_BORDER_SIZE - TFT_BUTTON_V_SIZE, TFT_BUTTON_H_SIZE, TFT_BUTTON_V_SIZE, TFT_FONT_02_SIZE, EVE_OPT_FORMAT, MENU_BACK, 0);
      EVE_cmd_dl(TAG(0));

      // Display footer
      TFT_display_footer();
      break;
    case 130:                                             // TRACKS setup
      EVE_cmd_dl(CMD_DLSTART);                            /* start the display list */
      EVE_cmd_dl(DL_CLEAR_RGB | BLACK);                   /* set the default clear color to white */
      EVE_cmd_dl(DL_CLEAR | CLR_COL | CLR_STN | CLR_TAG); /* clear the screen - this and the previous prevent artifacts between lists, Attributes are the color, stencil and tag buffers */
      EVE_cmd_dl(TAG(0));

      // insert static part of display-list from copy in gfx-mem
      EVE_cmd_append(MEM_DL_STATIC, num_dl_static);

      // Display date/time
      TFT_display_header();

      // Display ...
      if (g_trackQty > 0)
      {
        EVE_color_rgb(HEADERS);
        EVE_cmd_text(EVE_HSIZE / 12 * 2, TFT_HEADER_V_SPACE, TFT_FONT_02_SIZE, EVE_OPT_FORMAT, "ID");
        EVE_cmd_text(EVE_HSIZE / 12 * 4, TFT_HEADER_V_SPACE, TFT_FONT_02_SIZE, EVE_OPT_FORMAT, "NOM");
        if (fix_data.valid.location)
        {
          EVE_cmd_text(EVE_HSIZE / 12 * 8, TFT_HEADER_V_SPACE, TFT_FONT_02_SIZE, EVE_OPT_FORMAT, "DISTANCE");
        }
        EVE_color_rgb(TFT_DEFAULT_FONT_COLOR);
        for (uint8_t i = g_trackPage * TRACK_PAGINATION; i < (g_trackPage * TRACK_PAGINATION) + TRACK_PAGINATION; i++)
        {
          if (i < g_trackQty)
          {
            EVE_cmd_text_var(EVE_HSIZE / 12 * 2, TFT_HEADER_V_SPACE_HEADER + TFT_FONT_02_V_SPACE * (i - g_trackPage * TRACK_PAGINATION), TFT_FONT_02_SIZE, EVE_OPT_FORMAT, "%d", 1, g_tracksList[i].trackId);
            EVE_cmd_text(EVE_HSIZE / 12 * 4, TFT_HEADER_V_SPACE_HEADER + TFT_FONT_02_V_SPACE * (i - g_trackPage * TRACK_PAGINATION), TFT_FONT_02_SIZE, EVE_OPT_FORMAT, g_tracksList[i].trackName);
            if (fix_data.valid.location)
            {
              EVE_cmd_text_var(EVE_HSIZE / 12 * 8, TFT_HEADER_V_SPACE_HEADER + TFT_FONT_02_V_SPACE * (i - g_trackPage * TRACK_PAGINATION), TFT_FONT_02_SIZE, EVE_OPT_FORMAT, "%d", 1, g_tracksList[i].trackDistance);
            }
          }
        }
        EVE_cmd_text_var(EVE_HSIZE / 12 * 11, TFT_HEADER_V_SPACE_HEADER + TFT_FONT_02_V_SPACE * 7, TFT_FONT_02_SIZE, EVE_OPT_FORMAT, "%d/%d", 2, g_trackPage + 1, ((int)(g_trackQty / TRACK_PAGINATION)) + 1);
      }

      // Display setup menu buttons
      EVE_cmd_dl(DL_COLOR_RGB | WHITE);
      EVE_cmd_fgcolor(0x00c0c0c0); /* some grey */
      EVE_cmd_dl(TAG(130));
      EVE_cmd_button_var(TFT_BUTTON_BORDER_SIZE, EVE_VSIZE - TFT_BUTTON_BORDER_SIZE - TFT_BUTTON_V_SIZE, TFT_BUTTON_H_SIZE, TFT_BUTTON_V_SIZE, TFT_FONT_02_SIZE, EVE_OPT_FORMAT, MENU_BACK, 0);
      if (g_trackQty > TRACK_PAGINATION)
      {
        EVE_cmd_dl(TAG(131));
        EVE_cmd_button_var(TFT_BUTTON_BORDER_SIZE + (TFT_BUTTON_H_SIZE + TFT_BUTTON_H_SPACE), EVE_VSIZE - TFT_BUTTON_BORDER_SIZE - TFT_BUTTON_V_SIZE, TFT_BUTTON_H_SIZE, TFT_BUTTON_V_SIZE, TFT_FONT_02_SIZE, EVE_OPT_FORMAT, MENU_PREVIOUS, 0);
        EVE_cmd_dl(TAG(132));
        EVE_cmd_button_var(TFT_BUTTON_BORDER_SIZE + (TFT_BUTTON_H_SIZE + TFT_BUTTON_H_SPACE) * 2, EVE_VSIZE - TFT_BUTTON_BORDER_SIZE - TFT_BUTTON_V_SIZE, TFT_BUTTON_H_SIZE, TFT_BUTTON_V_SIZE, TFT_FONT_02_SIZE, EVE_OPT_FORMAT, MENU_NEXT, 0);
      }
      if (fix_data.valid.location && g_trackQty > 0)
      {
        EVE_cmd_dl(TAG(133));
        EVE_cmd_button_var(TFT_BUTTON_BORDER_SIZE + (TFT_BUTTON_H_SIZE + TFT_BUTTON_H_SPACE) * 3, EVE_VSIZE - TFT_BUTTON_BORDER_SIZE - TFT_BUTTON_V_SIZE, TFT_BUTTON_H2_SIZE, TFT_BUTTON_V_SIZE, TFT_FONT_02_SIZE, EVE_OPT_FORMAT, MENU_AUTOSELECT_TRACK, 0);
      }
      EVE_cmd_dl(TAG(0));

      // Display footer
      TFT_display_footer();
      break;
    case 140:                                             // EEPROM setup
      EVE_cmd_dl(CMD_DLSTART);                            /* start the display list */
      EVE_cmd_dl(DL_CLEAR_RGB | BLACK);                   /* set the default clear color to white */
      EVE_cmd_dl(DL_CLEAR | CLR_COL | CLR_STN | CLR_TAG); /* clear the screen - this and the previous prevent artifacts between lists, Attributes are the color, stencil and tag buffers */
      EVE_cmd_dl(TAG(0));

      // insert static part of display-list from copy in gfx-mem
      EVE_cmd_append(MEM_DL_STATIC, num_dl_static);

      // Display date/time
      TFT_display_header();

      // Display ...
      EVE_cmd_text_var(TFT_DEFAULT_BORDER_H_SIZE, TFT_DEFAULT_BORDER_V_SIZE + (TFT_FONT_01_V_SPACE)*2, TFT_FONT_01_SIZE, EVE_OPT_FORMAT, "g_rpmCorrectionRatio : %u", 1, g_rpmCorrectionRatio);
      EVE_cmd_text_var(TFT_DEFAULT_BORDER_H_SIZE, TFT_DEFAULT_BORDER_V_SIZE + (TFT_FONT_01_V_SPACE)*3, TFT_FONT_01_SIZE, EVE_OPT_FORMAT, "g_rpmFlywheelTeeth : %u", 1, g_rpmFlywheelTeeth);
      EVE_cmd_text_var(TFT_DEFAULT_BORDER_H_SIZE, TFT_DEFAULT_BORDER_V_SIZE + (TFT_FONT_01_V_SPACE)*4, TFT_FONT_01_SIZE, EVE_OPT_FORMAT, "g_trackQty : %u", 1, g_trackQty);
      EVE_cmd_text_var(TFT_DEFAULT_BORDER_H_SIZE, TFT_DEFAULT_BORDER_V_SIZE + (TFT_FONT_01_V_SPACE)*5, TFT_FONT_01_SIZE, EVE_OPT_FORMAT, "g_enDigitalInputsBits : %u", 1, g_enDigitalInputsBits);
      EVE_cmd_text_var(TFT_DEFAULT_BORDER_H_SIZE, TFT_DEFAULT_BORDER_V_SIZE + (TFT_FONT_01_V_SPACE)*6, TFT_FONT_01_SIZE, EVE_OPT_FORMAT, "g_enAnalogInputsBits : %u", 1, g_enAnalogInputsBits);
      EVE_cmd_text_var(TFT_DEFAULT_BORDER_H_SIZE, TFT_DEFAULT_BORDER_V_SIZE + (TFT_FONT_01_V_SPACE)*7, TFT_FONT_01_SIZE, EVE_OPT_FORMAT, "g_currentTrackId : %d", 1, g_currentTrackId);
      EVE_cmd_text_var(TFT_DEFAULT_BORDER_H_SIZE, TFT_DEFAULT_BORDER_V_SIZE + (TFT_FONT_01_V_SPACE)*8, TFT_FONT_01_SIZE, EVE_OPT_FORMAT, "g_enObd : %d", 1, g_enObd);

      // g_inAnaGearCalib & g_mlxAddresses
      EVE_cmd_text_var(220, TFT_DEFAULT_BORDER_V_SIZE + (TFT_FONT_01_V_SPACE)*2, TFT_FONT_01_SIZE, EVE_OPT_FORMAT, "g_inAnaGearCalib", 0);
      for (uint8_t i = 0; i < GEAR_CALIB_SIZE; i++)
      {
        EVE_cmd_text_var(220, TFT_DEFAULT_BORDER_V_SIZE + (TFT_FONT_01_V_SPACE) * (3 + i), TFT_FONT_01_SIZE, EVE_OPT_FORMAT, "%u", 1, g_inAnaGearCalib[i]);
      }
      EVE_cmd_text_var(360, TFT_DEFAULT_BORDER_V_SIZE + (TFT_FONT_01_V_SPACE)*2, TFT_FONT_01_SIZE, EVE_OPT_FORMAT, "g_mlxAddresses", 0);
      for (uint8_t i = 0; i < MAX_MLX_SIZE; i++)
      {
        EVE_cmd_text_var(360, TFT_DEFAULT_BORDER_V_SIZE + (TFT_FONT_01_V_SPACE) * (3 + i), TFT_FONT_01_SIZE, EVE_OPT_FORMAT, "%u", 1, g_mlxAddresses[i]);
      }

      // Display setup menu buttons
      EVE_cmd_dl(DL_COLOR_RGB | WHITE);
      EVE_cmd_fgcolor(0x00c0c0c0); /* some grey */
      EVE_cmd_dl(TAG(140));
      EVE_cmd_button_var(TFT_BUTTON_BORDER_SIZE, EVE_VSIZE - TFT_BUTTON_BORDER_SIZE - TFT_BUTTON_V_SIZE, TFT_BUTTON_H_SIZE, TFT_BUTTON_V_SIZE, TFT_FONT_02_SIZE, EVE_OPT_FORMAT, MENU_BACK, 0);
      EVE_cmd_dl(TAG(141));
      EVE_cmd_button_var(TFT_BUTTON_BORDER_SIZE + (TFT_BUTTON_H_SIZE + TFT_BUTTON_H_SPACE), EVE_VSIZE - TFT_BUTTON_BORDER_SIZE - TFT_BUTTON_V_SIZE, TFT_BUTTON_H_SIZE, TFT_BUTTON_V_SIZE, TFT_FONT_02_SIZE, EVE_OPT_FORMAT, MENU_RESET_EEPROM, 0);
      EVE_cmd_dl(TAG(142));
      EVE_cmd_button_var(TFT_BUTTON_BORDER_SIZE + (TFT_BUTTON_H_SIZE + TFT_BUTTON_H_SPACE) * 2, EVE_VSIZE - TFT_BUTTON_BORDER_SIZE - TFT_BUTTON_V_SIZE, TFT_BUTTON_H_SIZE, TFT_BUTTON_V_SIZE, TFT_FONT_02_SIZE, EVE_OPT_FORMAT, MENU_DEFAULT_EEPROM, 0);
      EVE_cmd_dl(TAG(0));

      // Display footer
      TFT_display_footer();
      break;
    case 150:                                             // LAP TIMES
      EVE_cmd_dl(CMD_DLSTART);                            /* start the display list */
      EVE_cmd_dl(DL_CLEAR_RGB | BLACK);                   /* set the default clear color to white */
      EVE_cmd_dl(DL_CLEAR | CLR_COL | CLR_STN | CLR_TAG); /* clear the screen - this and the previous prevent artifacts between lists, Attributes are the color, stencil and tag buffers */
      EVE_cmd_dl(TAG(0));

      // insert static part of display-list from copy in gfx-mem
      EVE_cmd_append(MEM_DL_STATIC, num_dl_static);

      // Display date/time
      TFT_display_header();

      // Display ...
      if (g_lapQty > 0)
      {
        EVE_color_rgb(HEADERS);
        EVE_cmd_text(EVE_HSIZE / 12, TFT_HEADER_V_SPACE, TFT_FONT_01_SIZE, EVE_OPT_FORMAT, "LAP");
        EVE_cmd_text(EVE_HSIZE / 12 * 2, TFT_HEADER_V_SPACE, TFT_FONT_01_SIZE, EVE_OPT_FORMAT, "LAPTIME");
        EVE_cmd_text(EVE_HSIZE / 12 * 4, TFT_HEADER_V_SPACE, TFT_FONT_01_SIZE, EVE_OPT_FORMAT, "SPD");
        EVE_cmd_text(EVE_HSIZE / 12 * 5, TFT_HEADER_V_SPACE, TFT_FONT_01_SIZE, EVE_OPT_FORMAT, "DATE");
        EVE_cmd_text(EVE_HSIZE / 12 * 10, TFT_HEADER_V_SPACE, TFT_FONT_01_SIZE, EVE_OPT_FORMAT, "TRACK");
        EVE_color_rgb(TFT_DEFAULT_FONT_COLOR);

        for (uint8_t i = g_lapPage * LAP_PAGINATION; i < (g_lapPage * LAP_PAGINATION) + LAP_PAGINATION; i++)
        {
          if (i < g_lapQty) // && g_lapsList[i].lapTime > 0
          {
            getTrackName(g_lapsList[i].lapTrackId);    // Store track name in "g_trackName" global var
            g_date = g_lapsList[i].lapStartTimestampS; // Store timestamp in a "date" type var
            if (g_lapsList[i].lapIsBest == true)       // Set green color for best lap
            {
              EVE_color_rgb(GREEN);
            }
            else
            {
              EVE_color_rgb(TFT_DEFAULT_FONT_COLOR);
            }
            EVE_cmd_text_var(EVE_HSIZE / 12, TFT_HEADER_V_SPACE_HEADER + TFT_FONT_01_V_SPACE * (i - g_lapPage * LAP_PAGINATION), TFT_FONT_01_SIZE, EVE_OPT_FORMAT, "%u", 1, g_lapsList[i].lapNumber);
            EVE_cmd_text_var(EVE_HSIZE / 12 * 2, TFT_HEADER_V_SPACE_HEADER + TFT_FONT_01_V_SPACE * (i - g_lapPage * LAP_PAGINATION), TFT_FONT_01_SIZE, EVE_OPT_FORMAT, "%02u:%02u:%02u", 3, g_lapsList[i].lapTimeS / 60, g_lapsList[i].lapTimeS % 60, g_lapsList[i].lapTimeCs);
            EVE_cmd_text_var(EVE_HSIZE / 12 * 4, TFT_HEADER_V_SPACE_HEADER + TFT_FONT_01_V_SPACE * (i - g_lapPage * LAP_PAGINATION), TFT_FONT_01_SIZE, EVE_OPT_FORMAT, "%u", 1, g_lapsList[i].lapMaxSpeed);
            EVE_cmd_text_var(EVE_HSIZE / 12 * 5, TFT_HEADER_V_SPACE_HEADER + TFT_FONT_01_V_SPACE * (i - g_lapPage * LAP_PAGINATION), TFT_FONT_01_SIZE, EVE_OPT_FORMAT, "%02u/%02u/%02u %02u:%02u:%02u", 6, day(g_date), month(g_date), year(g_date), hour(g_date), minute(g_date), second(g_date));
            EVE_cmd_text(EVE_HSIZE / 12 * 10, TFT_HEADER_V_SPACE_HEADER + TFT_FONT_01_V_SPACE * (i - g_lapPage * LAP_PAGINATION), TFT_FONT_01_SIZE, EVE_OPT_FORMAT, g_trackName);
          }
        }
        EVE_color_rgb(TFT_DEFAULT_FONT_COLOR);
        EVE_cmd_text_var(EVE_HSIZE / 12 * 11, TFT_HEADER_V_SPACE_HEADER + TFT_FONT_02_V_SPACE * 7, TFT_FONT_02_SIZE, EVE_OPT_FORMAT, "%d/%d", 2, g_lapPage + 1, ((int)(g_lapQty / LAP_PAGINATION)) + 1);
      }

      // Display setup menu buttons
      EVE_cmd_dl(DL_COLOR_RGB | WHITE);
      EVE_cmd_fgcolor(0x00c0c0c0); /* some grey */
      EVE_cmd_dl(TAG(150));
      EVE_cmd_button_var(TFT_BUTTON_BORDER_SIZE, EVE_VSIZE - TFT_BUTTON_BORDER_SIZE - TFT_BUTTON_V_SIZE, TFT_BUTTON_H_SIZE, TFT_BUTTON_V_SIZE, TFT_FONT_02_SIZE, EVE_OPT_FORMAT, MENU_BACK, 0);
      EVE_cmd_dl(TAG(151));
      EVE_cmd_button_var(TFT_BUTTON_BORDER_SIZE + (TFT_BUTTON_H_SIZE + TFT_BUTTON_H_SPACE) * 3, EVE_VSIZE - TFT_BUTTON_BORDER_SIZE - TFT_BUTTON_V_SIZE, TFT_BUTTON_H_SIZE, TFT_BUTTON_V_SIZE, TFT_FONT_02_SIZE, EVE_OPT_FORMAT, MENU_BEST_LT_72H, 0);
      EVE_cmd_dl(TAG(152));
      EVE_cmd_button_var(TFT_BUTTON_BORDER_SIZE + (TFT_BUTTON_H_SIZE + TFT_BUTTON_H_SPACE), EVE_VSIZE - TFT_BUTTON_BORDER_SIZE - TFT_BUTTON_V_SIZE, TFT_BUTTON_H_SIZE, TFT_BUTTON_V_SIZE, TFT_FONT_02_SIZE, EVE_OPT_FORMAT, MENU_BEST_LT_TRACK, 0);
      EVE_cmd_dl(TAG(153));
      EVE_cmd_button_var(TFT_BUTTON_BORDER_SIZE + (TFT_BUTTON_H_SIZE + TFT_BUTTON_H_SPACE) * 2, EVE_VSIZE - TFT_BUTTON_BORDER_SIZE - TFT_BUTTON_V_SIZE, TFT_BUTTON_H_SIZE, TFT_BUTTON_V_SIZE, TFT_FONT_02_SIZE, EVE_OPT_FORMAT, MENU_BEST_LT_ALL_TRK, 0);
      EVE_cmd_dl(TAG(154));
      EVE_cmd_button_var(TFT_BUTTON_BORDER_SIZE + (TFT_BUTTON_H_SIZE + TFT_BUTTON_H_SPACE) * 4, EVE_VSIZE - TFT_BUTTON_BORDER_SIZE - TFT_BUTTON_V_SIZE, TFT_BUTTON_H_SIZE, TFT_BUTTON_V_SIZE, TFT_FONT_02_SIZE, EVE_OPT_FORMAT, MENU_BEST_LT_LASTRUN, 0);
      // Best (current track)
      // Best (1 for each track)
      // Best last 24h
      // Best last 7 days
      if (g_lapQty > LAP_PAGINATION)
      {
        EVE_cmd_dl(TAG(151));
        EVE_cmd_button_var(TFT_BUTTON_BORDER_SIZE + (TFT_BUTTON_H_SIZE + TFT_BUTTON_H_SPACE), EVE_VSIZE - TFT_BUTTON_BORDER_SIZE - TFT_BUTTON_V_SIZE, TFT_BUTTON_H_SIZE, TFT_BUTTON_V_SIZE, TFT_FONT_02_SIZE, EVE_OPT_FORMAT, MENU_PREVIOUS, 0);
        EVE_cmd_dl(TAG(152));
        EVE_cmd_button_var(TFT_BUTTON_BORDER_SIZE + (TFT_BUTTON_H_SIZE + TFT_BUTTON_H_SPACE) * 2, EVE_VSIZE - TFT_BUTTON_BORDER_SIZE - TFT_BUTTON_V_SIZE, TFT_BUTTON_H_SIZE, TFT_BUTTON_V_SIZE, TFT_FONT_02_SIZE, EVE_OPT_FORMAT, MENU_NEXT, 0);
      }
      EVE_cmd_dl(TAG(0));

      // Display footer
      TFT_display_footer();
      break;
    default:                                              // If no tagged button (safe mode)
      EVE_cmd_dl(CMD_DLSTART);                            /* start the display list */
      EVE_cmd_dl(DL_CLEAR_RGB | BLACK);                   /* set the default clear color to white */
      EVE_cmd_dl(DL_CLEAR | CLR_COL | CLR_STN | CLR_TAG); /* clear the screen - this and the previous prevent artifacts between lists, Attributes are the color, stencil and tag buffers */
      EVE_cmd_dl(TAG(0));

      // Display setup menu buttons
      EVE_cmd_dl(DL_COLOR_RGB | WHITE);
      EVE_cmd_fgcolor(0x00c0c0c0); /* some grey */
      EVE_cmd_dl(TAG(50));
      EVE_cmd_button_var(TFT_BUTTON_BORDER_SIZE, EVE_VSIZE - TFT_BUTTON_BORDER_SIZE - TFT_BUTTON_V_SIZE, TFT_BUTTON_H_SIZE, TFT_BUTTON_V_SIZE, 13, EVE_OPT_FORMAT, MENU_BACK, 0);
      EVE_cmd_dl(TAG(0));

      // Display footer
      TFT_display_footer();
      break;
    }

    EVE_cmd_dl(DL_DISPLAY); /* instruct the graphics processor to show the list */
    EVE_cmd_dl(CMD_SWAP);   /* make this list active */
  }
}

/*EVE_start_cmd_burst();
EVE_cmd_dl_burst(CMD_DLSTART);                
EVE_cmd_dl_burst(DL_CLEAR_RGB | WHITE);         
EVE_cmd_dl_burst(DL_CLEAR | CLR_COL | CLR_STN | CLR_TAG); 
EVE_cmd_dl_burst(TAG(0));
EVE_cmd_append_burst(MEM_DL_STATIC, num_dl_static);
EVE_color_rgb_burst(WHITE);
EVE_cmd_fgcolor_burst(0x00c0c0c0); 
EVE_cmd_dl_burst(TAG(10));      
EVE_cmd_button_burst(20, 20, 80, 30, 28, toggle_state, "Touch!");
EVE_cmd_dl_burst(TAG(0)); 
EVE_cmd_dl_burst(DL_COLOR_RGB | BLACK);
EVE_cmd_button_burst(20, 120, 80, 30, 28, 0, "Touch!");
EVE_cmd_setfont2_burst(12, MEM_FONT_01, 32);
EVE_cmd_text_burst(10, 160, 12, 0, "LOOP - The quick brown fox");
EVE_cmd_text_burst(10, 80, 12, 0, "Hello UTF-8: €µäöü"); //€µ°");
EVE_color_rgb_burst(BLACK);
EVE_cmd_dl_burst(DL_DISPLAY);
EVE_cmd_dl_burst(CMD_SWAP);  
EVE_end_cmd_burst();*/
