quichedood/DAWA-7.x/03-DEV/include/tft.h

#ifndef TFT_H_
#define TFT_H_

void TFT_init(void);
void TFT_touch(void);
void TFT_display(void);
void TFT_display_header(void);
void TFT_display_footer(void);
void TFT_display_setup_buttons(void);

#endif /* TFT_H_ */
